v01dma1n/TemporalAnomalyClock/images/input/Gemini_Generated_Image_8mpy4m8mpy4m8mpy.png

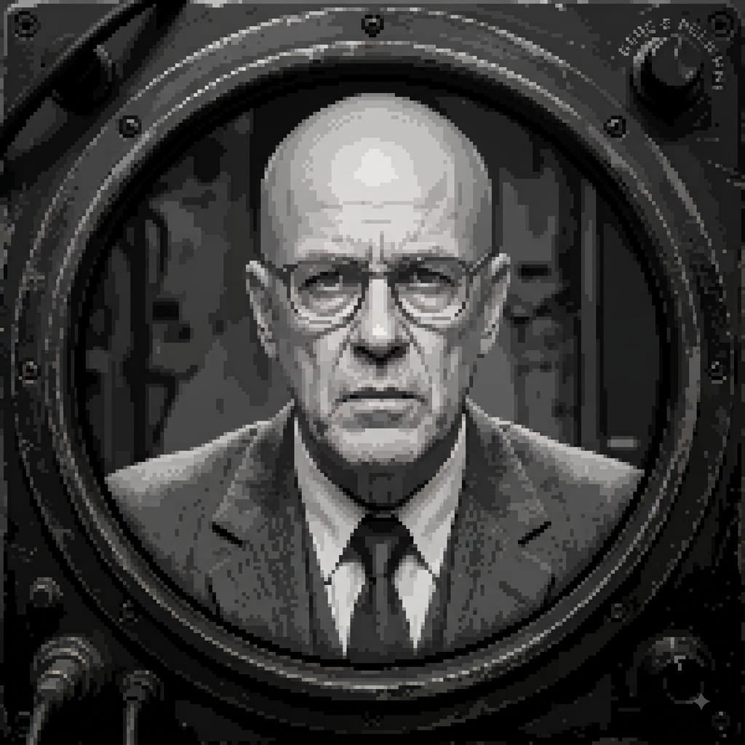
images/input/Gemini_Generated_Image_8mpy4m8mpy4m8mpy.png
