v01dma1n/TemporalAnomalyClock/print3d/Temporal Anomaly DisplayCase - V1 Display Case Test.step

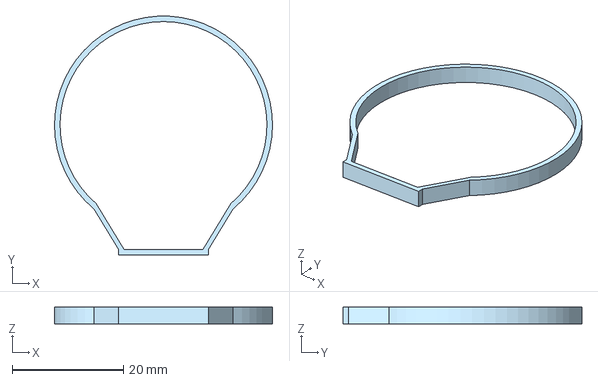
[picture p20: CAD file, 2026-08-07]
print3d/Temporal Anomaly DisplayCase - V1 Display Case Test.step
39.2 x 43.0 x 3.00 mm
