v01dma1n/TemporalAnomalyClock/print3d/Temporal Anomaly Lens Mount - V4 Lens Mount.step

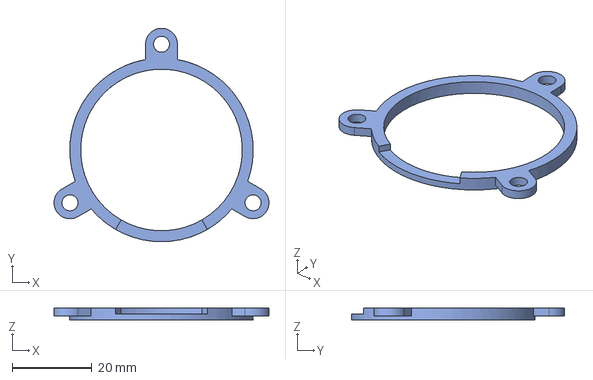
[picture p21: CAD file, 2026-08-07]
print3d/Temporal Anomaly Lens Mount - V4 Lens Mount.step
53.9 x 53.5 x 3.00 mm
